mjoldfield/ir-morse-toys/rx-bb/hardware/bb.kicad_sch

## KiCad design rx-bb/hardware/bb.kicad_sch (2022-05-23)

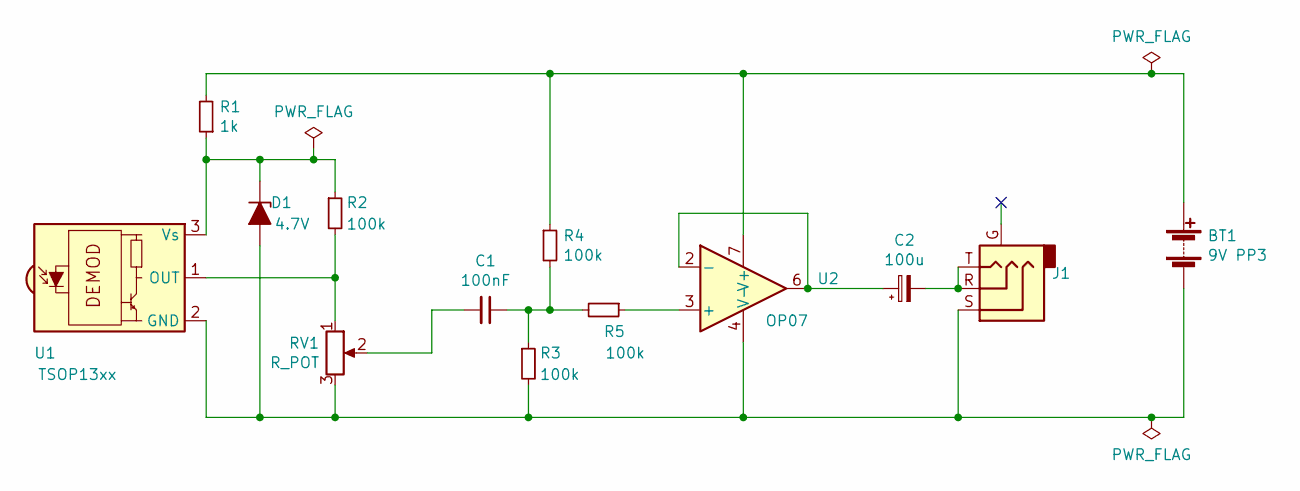
[picture p9: schematic bb.kicad_sch]

Parts:
BT1: 9V PP3; Battery_Keystone_968
C1: 100nF; C_Disc_D10.0mm_W2.5mm_P5.00mm
C2: 100u; CP_Radial_D6.3mm_P2.50mm
D1: 4.7V
J1: AudioJack3_Ground; TruConnect_3.5mm_StereoSocket
R1: 1k
R2, R3, R4, R5: 100k; R_Axial_DIN0207_L6.3mm_D2.5mm_P10.16mm_Horizontal
RV1: R_POT; Potentiometer_Piher_PC-16_Single_Horizontal
U1: TSOP13xx; Vishay_MINIMOLD-3Pin
U2: OP07; DIP-8_W7.62mm_Socket

Connections:
unnamed: BT1.1 (+), R1.2, R4.1, U2.7 (V+)
unnamed: BT1.2 (-), D1.2 (A), J1.S, R3.2, RV1.3, U1.2 (GND), U2.4 (V-)
unnamed: C1.1, R3.1, R4.2, R5.2
unnamed: C1.2, RV1.2
unnamed: C2.1, U2.2 (-), U2.6
unnamed: C2.2, J1.R, J1.T
unnamed: D1.1 (K), R1.1, R2.1, U1.3 (Vs)
unnamed: R2.2, RV1.1, U1.1 (OUT)
unnamed: R5.1, U2.3 (+)
